spstack/lightlink-remote-outlet/code/lightlink.X/config.h

/* 
 * @brief Top level config.h file that will simply include the device specific config header
 * @author Scott
 
 */

#ifndef CONFIG_H
#define	CONFIG_H

#ifdef	__cplusplus
extern "C" {
#endif

#include "config_16F18146.h"


#ifdef	__cplusplus
}
#endif

#endif	/* CONFIG_H */
