spstack/lightlink-remote-outlet/code/lightlink.X/eusart.h

/**
  EUSART Generated Driver API Header File

  @Company
    Microchip Technology Inc.

  @File Name
    eusart.h

  @Summary
    This is the generated header file for the EUSART driver using PIC10 / PIC12 / PIC16 / PIC18 MCUs

  @Description
    This header file provides APIs for driver for EUSART.
    Generation Information :
        Product Revision  :  PIC10 / PIC12 / PIC16 / PIC18 MCUs - 1.65
        Device            :  PIC16LF1455
        Driver Version    :  2.00
    The generated drivers are tested against the following:
        Compiler          :  XC8 1.45
        MPLAB 	          :  MPLAB X 4.10
*/
/*
    (c) 2016 Microchip Technology Inc. and its subsidiaries. You may use this
    software and any derivatives exclusively with Microchip products.

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
    IN NO EVENT WILL MICROCHIP BE LIABLE FOR ANY INDIRECT, SPECIAL, PUNITIVE,
    INCIDENTAL OR CONSEQUENTIAL LOSS, DAMAGE, COST OR EXPENSE OF ANY KIND
    WHATSOEVER RELATED TO THE SOFTWARE, HOWEVER CAUSED, EVEN IF MICROCHIP HAS
    BEEN ADVISED OF THE POSSIBILITY OR THE DAMAGES ARE FORESEEABLE. TO THE
    FULLEST EXTENT ALLOWED BY LAW, MICROCHIP'S TOTAL LIABILITY ON ALL CLAIMS IN
    ANY WAY RELATED TO THIS SOFTWARE WILL NOT EXCEED THE AMOUNT OF FEES, IF ANY,
    THAT YOU HAVE PAID DIRECTLY TO MICROCHIP FOR THIS SOFTWARE.

    MICROCHIP PROVIDES THIS SOFTWARE CONDITIONALLY UPON YOUR ACCEPTANCE OF THESE
    TERMS.
*/
#ifndef _EUSART_H
#define _EUSART_H

/**
  Section: Included Files
*/

#include <xc.h>
#include <stdbool.h>
#include <stdint.h>
#include <stdio.h>

#ifdef __cplusplus  // Provide C++ Compatibility

    extern "C" {

#endif


/**
  Section: Macro Declarations
*/

#define EUSART_DataReady  (PIR1bits.RCIF)


/**
  Section: EUSART APIs
*/

/**
  @Summary
    Initialization routine that takes inputs from the EUSART GUI.

  @Description
    This routine initializes the EUSART driver.
    This routine must be called before any other EUSART routine is called.

  @Preconditions
    None

  @Param
    None

  @Returns
    None

  @Comment
    
*/
void EUSART_Initialize(void);

/**
  @Summary
    Read a byte of data from the EUSART.

  @Description
    This routine reads a byte of data from the EUSART.

  @Preconditions
    EUSART_Initialize() function should have been called
    before calling this function. The transfer status should be checked to see
    if the receiver is not empty before calling this function.

  @Param
    None

  @Returns
    A data byte received by the driver.
*/
uint8_t EUSART_Read(void);

 /**
  @Summary
    Writes a byte of data to the EUSART.

  @Description
    This routine writes a byte of data to the EUSART.

  @Preconditions
    EUSART_Initialize() function should have been called
    before calling this function. The transfer status should be checked to see
    if transmitter is not busy before calling this function.

  @Param
    txData  - Data byte to write to the EUSART

  @Returns
    None
*/
void EUSART_Write(uint8_t txData);



#ifdef __cplusplus  // Provide C++ Compatibility

    }

#endif

#endif  // _EUSART_H
/**
 End of File
*/
